ilikecake/ESP32-Wall-Display/assets/placement_back.JPG

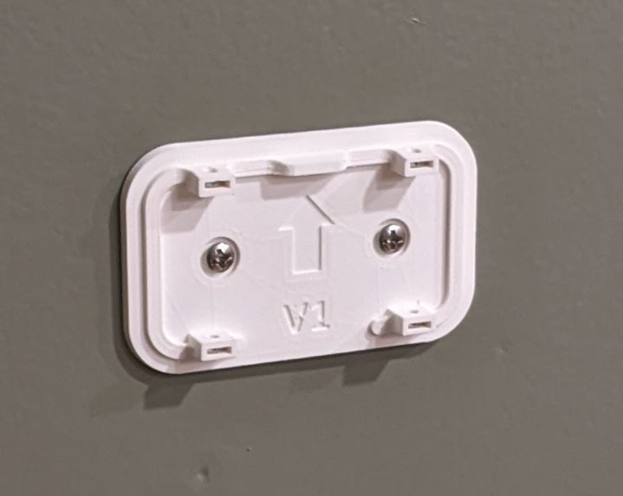
assets/placement_back.JPG
