ilikecake/ESP32-Wall-Display/assets/placement_front.JPG

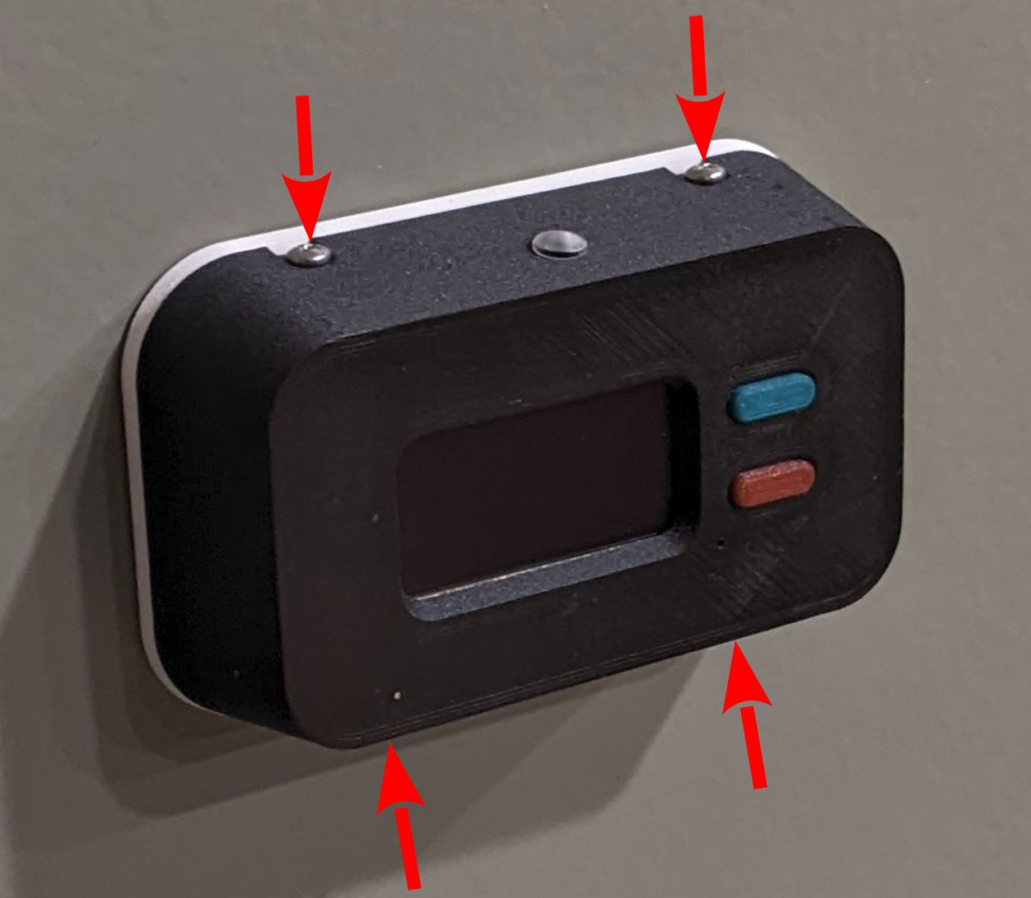
assets/placement_front.JPG
