ilikecake/ESP32-Wall-Display/assets/BOM_5.1K_Resistor.jpg

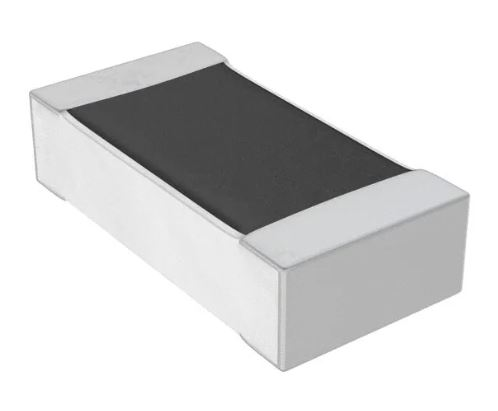
assets/BOM_5.1K_Resistor.jpg
