ilikecake/ESP32-Wall-Display/assets/BOM_Feather_ESP32-S3.jpg

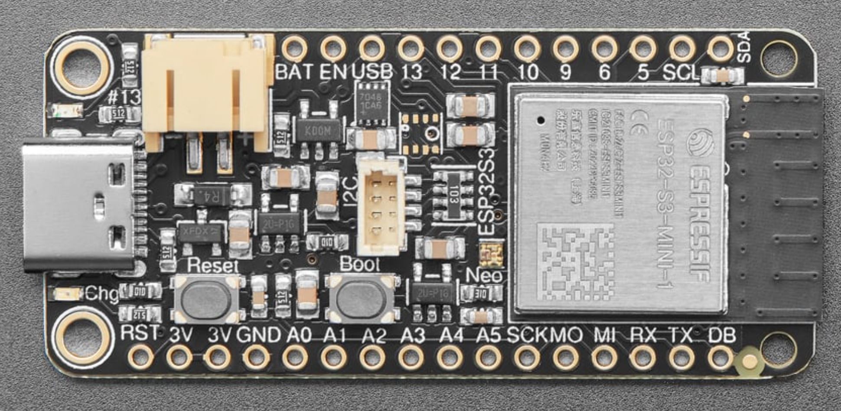
assets/BOM_Feather_ESP32-S3.jpg
