ilikecake/ESP32-Wall-Display/assets/BOM_Feather_Female_Headers.jpg

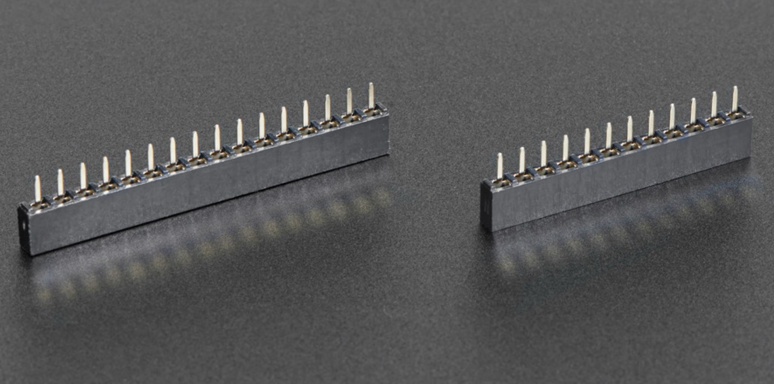
assets/BOM_Feather_Female_Headers.jpg
