ilikecake/ESP32-Wall-Display/assets/BOM_Feather_OLED_128x64.JPG

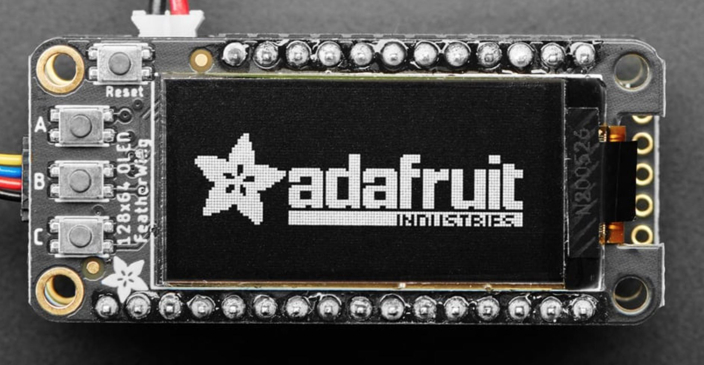
assets/BOM_Feather_OLED_128x64.JPG
