ilikecake/ESP32-Wall-Display/assets/BOM_Lightpipe.jpg

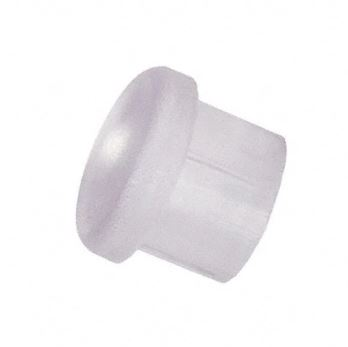
assets/BOM_Lightpipe.jpg
