ilikecake/ESP32-Wall-Display/assets/BOM_Neopixel.jpg

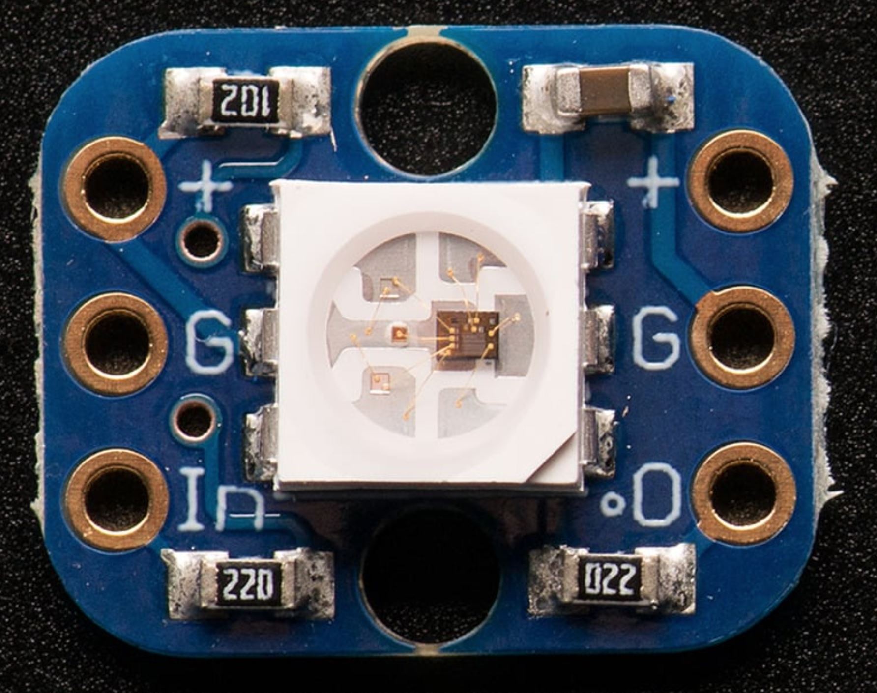
assets/BOM_Neopixel.jpg
