ilikecake/ESP32-Wall-Display/assets/BOM_Stemma_QT_Cable.jpg

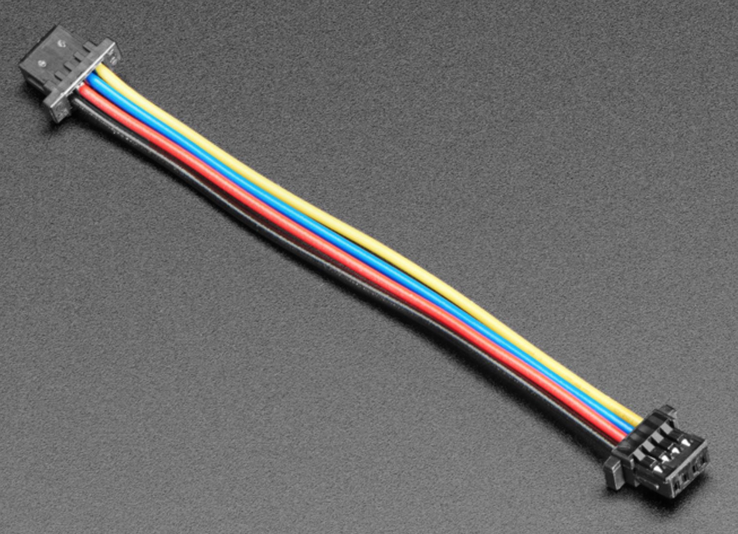
assets/BOM_Stemma_QT_Cable.jpg
