ilikecake/ESP32-Wall-Display/assets/BOM_USB_PCB.jpg

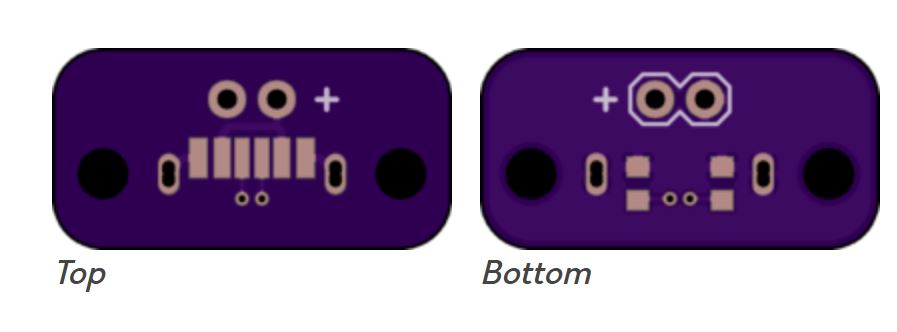
assets/BOM_USB_PCB.jpg
