ilikecake/ESP32-Wall-Display/assets/BOM_Wire.jpg

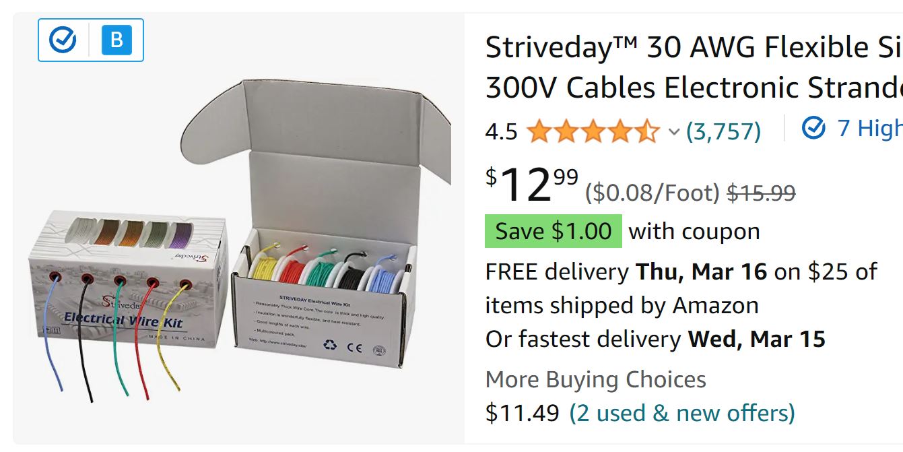
assets/BOM_Wire.jpg
