ilikecake/ESP32-Wall-Display/assets/assembly_step1_back.JPG

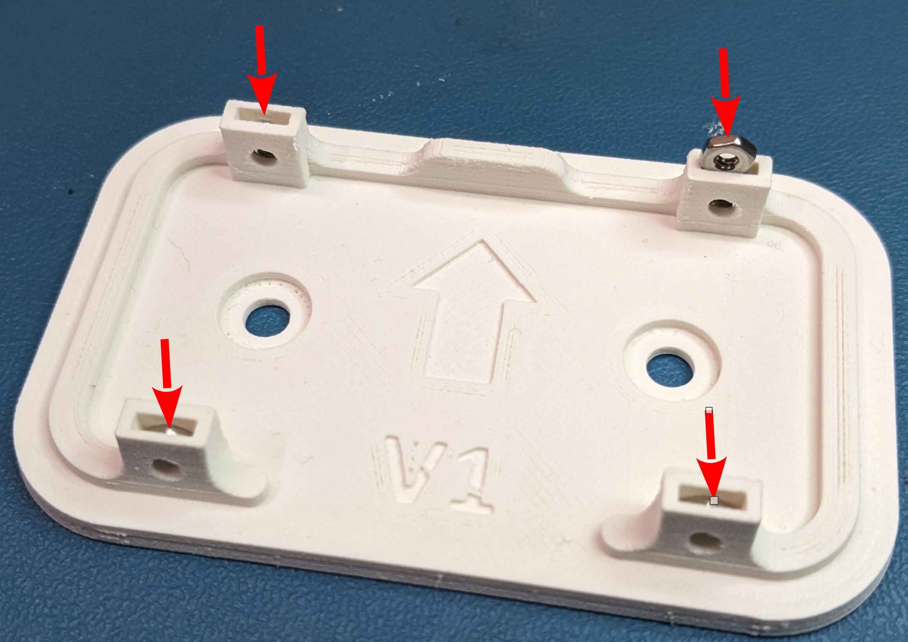
assets/assembly_step1_back.JPG
