ilikecake/ESP32-Wall-Display/assets/assembly_step1_front.JPG

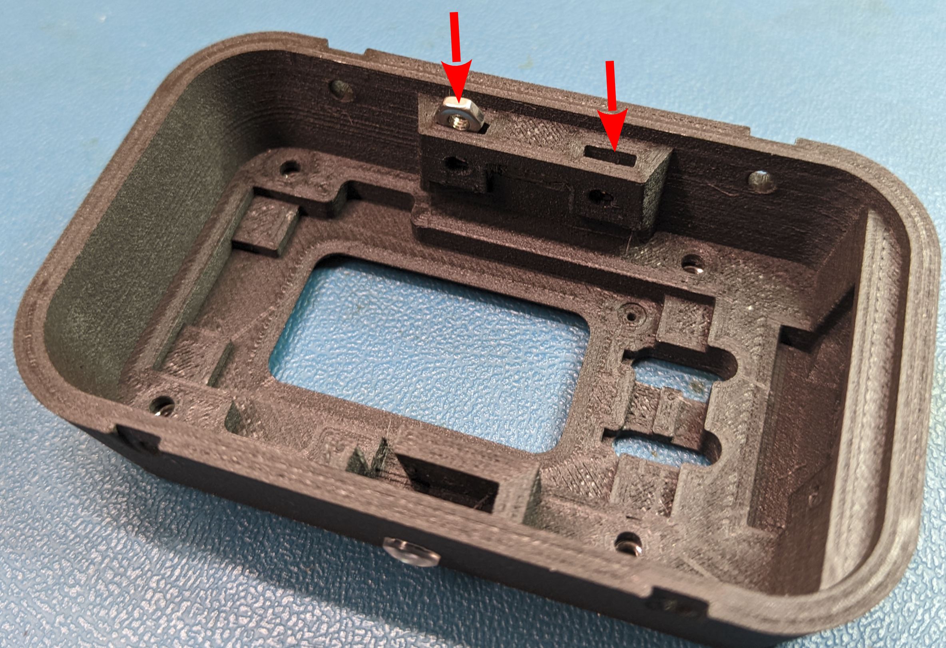
assets/assembly_step1_front.JPG
