ilikecake/ESP32-Wall-Display/assets/assembly_step2_lightpipe.JPG

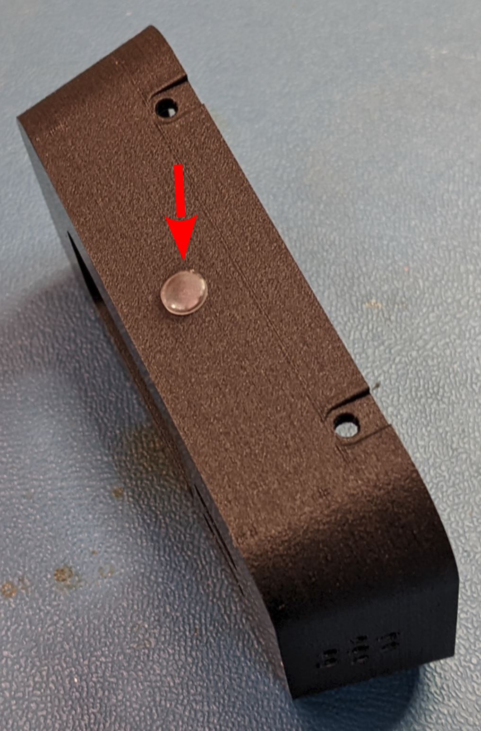
assets/assembly_step2_lightpipe.JPG
