ilikecake/ESP32-Wall-Display/assets/assembly_step3_buttons.JPG

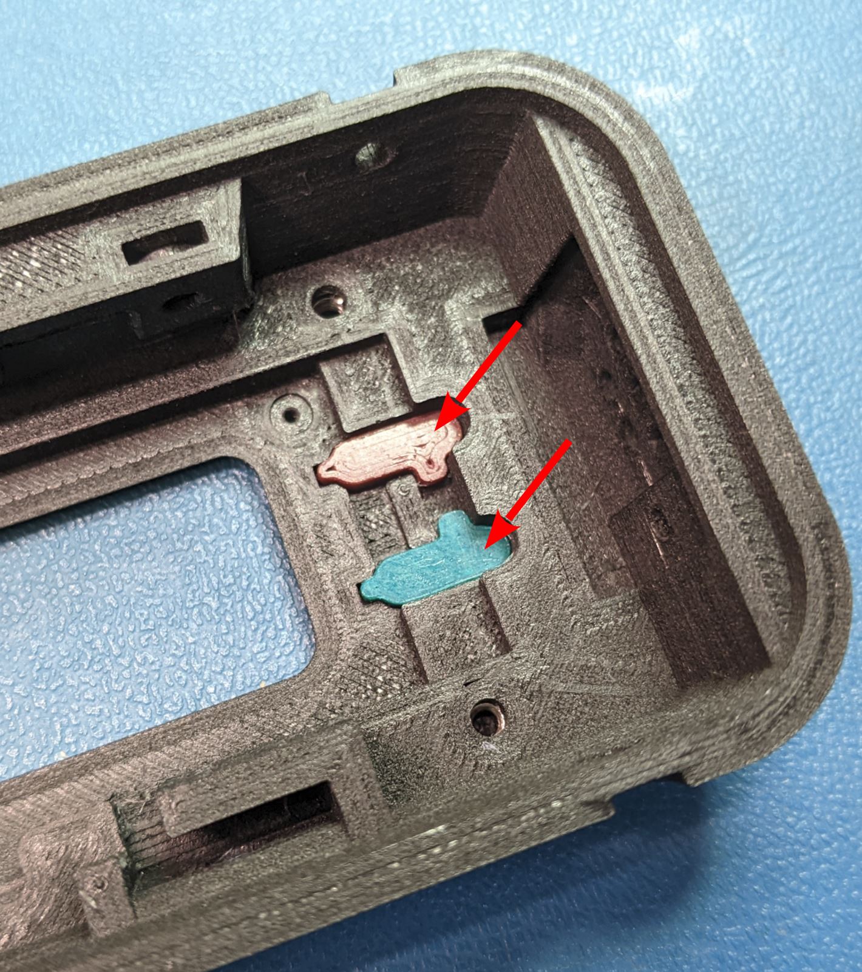
assets/assembly_step3_buttons.JPG
