ilikecake/ESP32-Wall-Display/assets/assembly_step4_power_wires.JPG

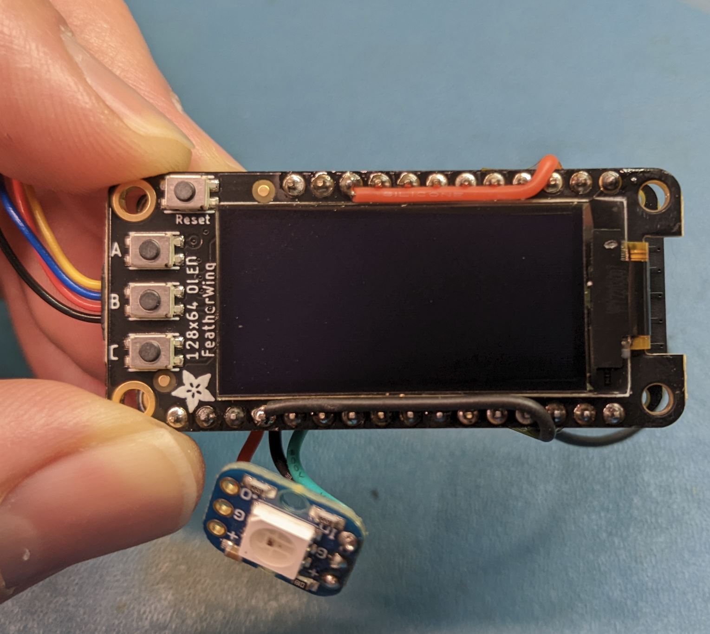
assets/assembly_step4_power_wires.JPG
