ilikecake/ESP32-Wall-Display/assets/assembly_step5_USB_port.JPG

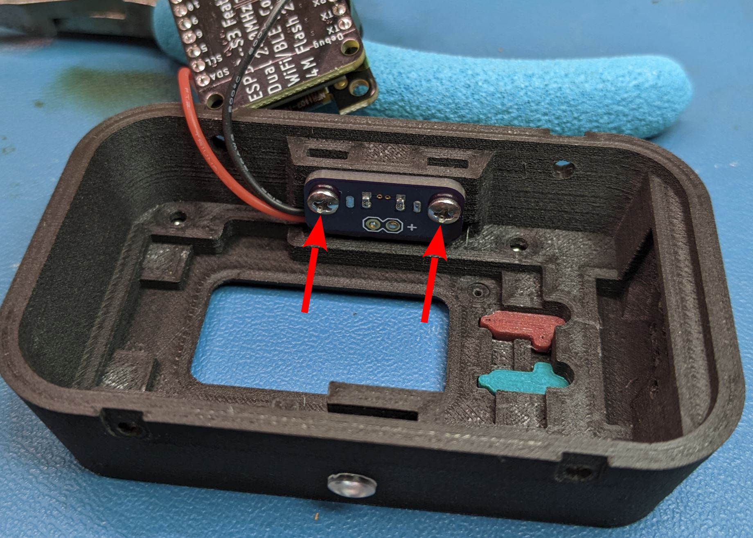
assets/assembly_step5_USB_port.JPG
