ilikecake/ESP32-Wall-Display/assets/assembly_step6_BME280.JPG

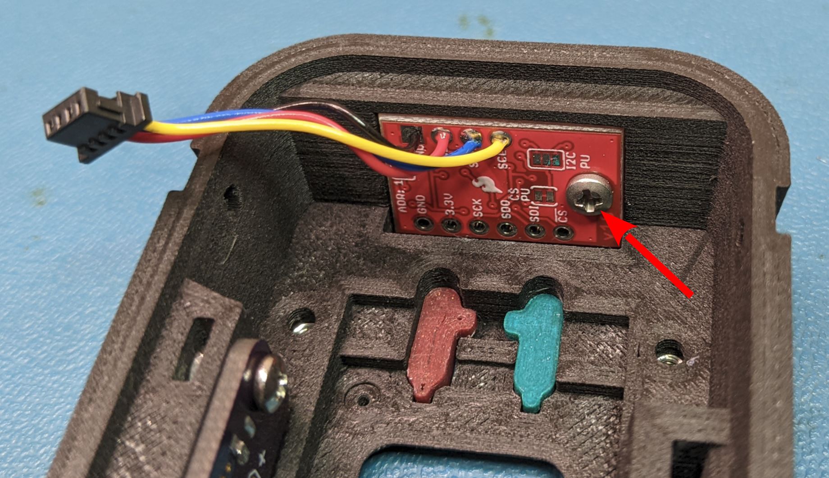
assets/assembly_step6_BME280.JPG
