ilikecake/ESP32-Wall-Display/assets/assembly_step7_display.JPG

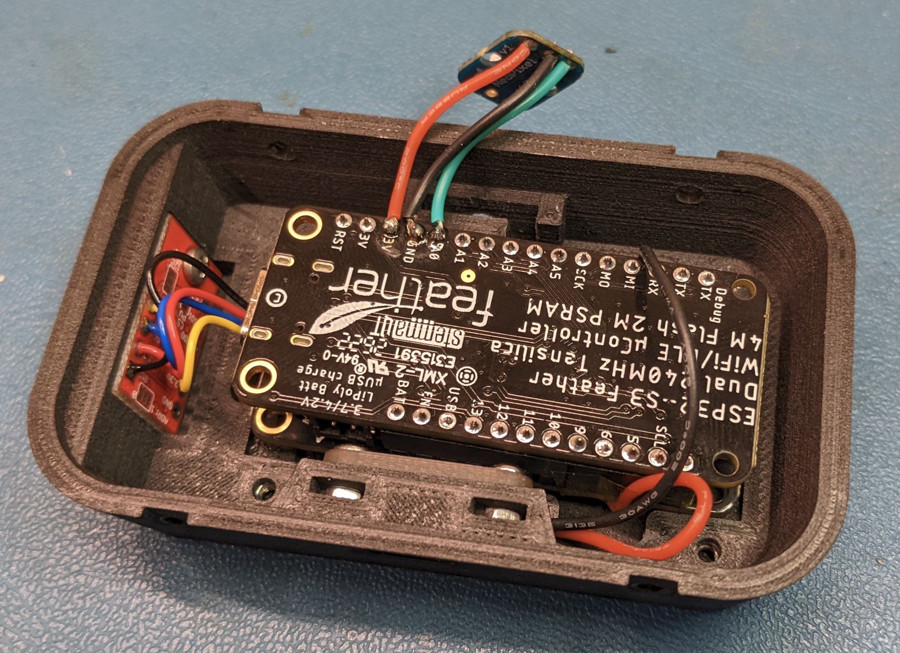
assets/assembly_step7_display.JPG
