ilikecake/ESP32-Wall-Display/assets/assembly_step7_long_support.JPG

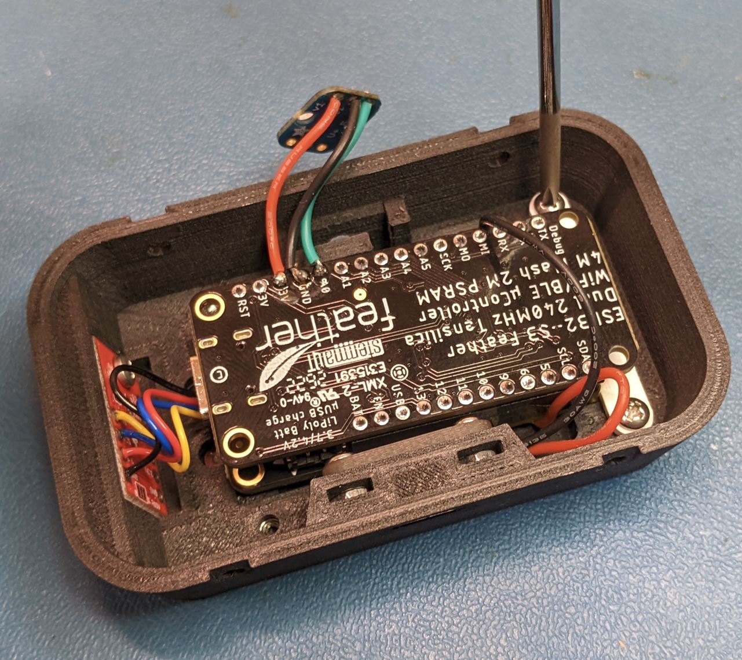
assets/assembly_step7_long_support.JPG
