ilikecake/ESP32-Wall-Display/assets/assembly_step7_short_support.JPG

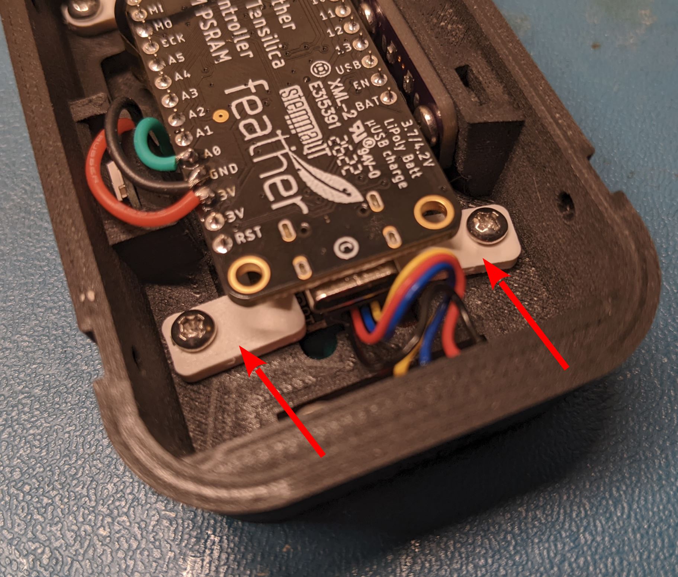
assets/assembly_step7_short_support.JPG
