ilikecake/ESP32-Wall-Display/assets/assembly_step8_LED1.JPG

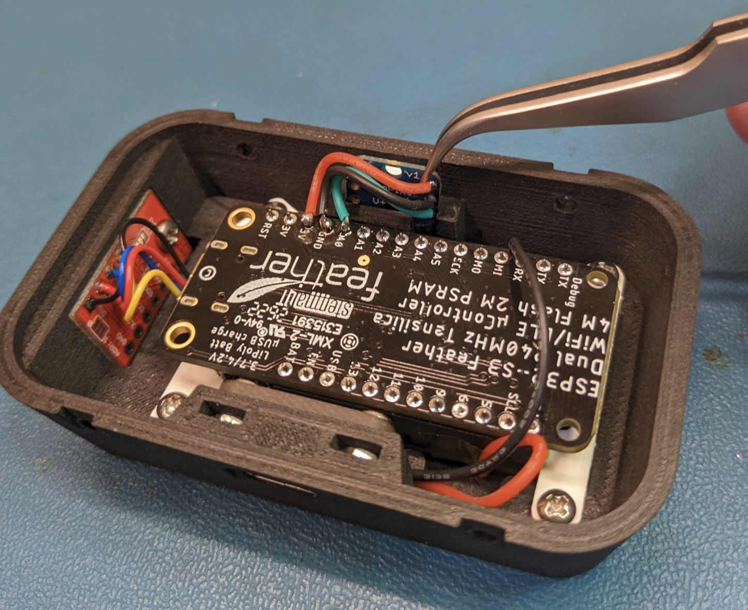
assets/assembly_step8_LED1.JPG
