ilikecake/ESP32-Wall-Display/assets/assembly_step8_LED2.JPG

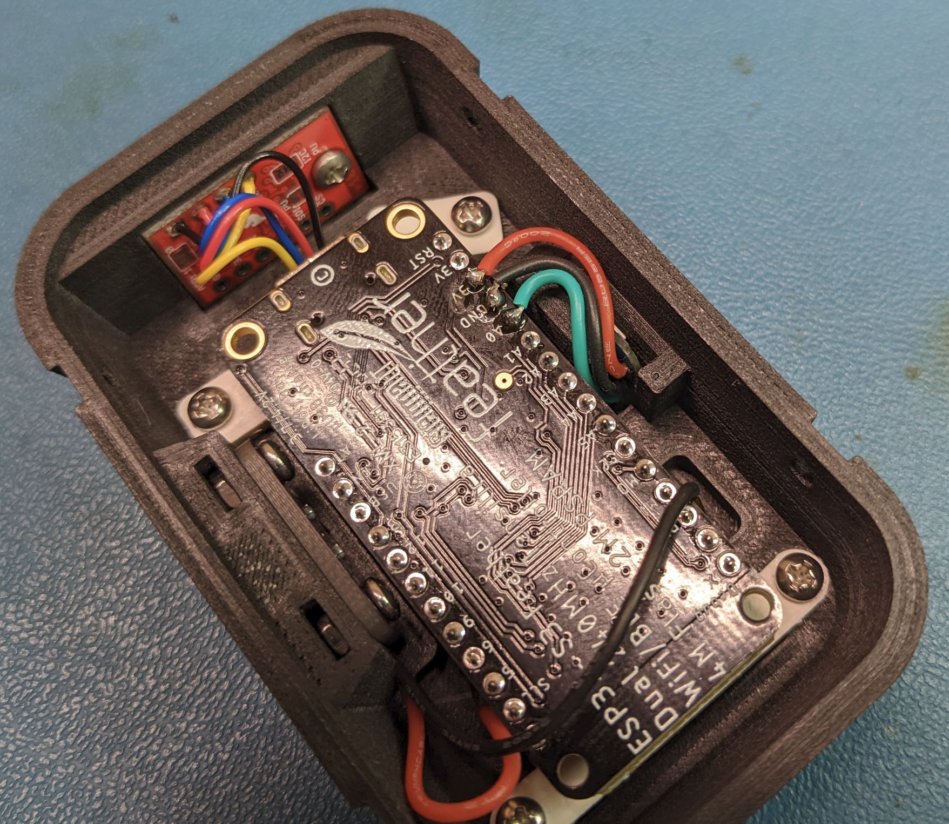
assets/assembly_step8_LED2.JPG
