ilikecake/ESP32-Wall-Display/assets/Printing_Button1.JPG

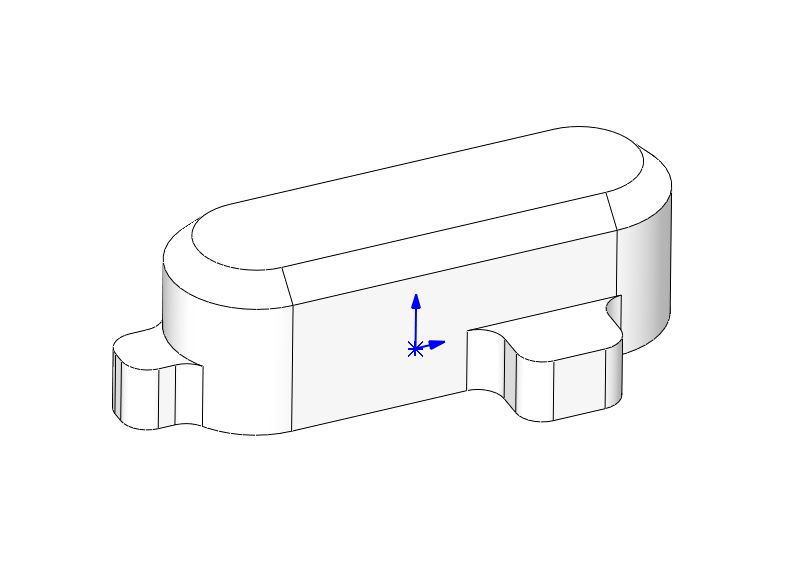
assets/Printing_Button1.JPG
