ilikecake/ESP32-Wall-Display/assets/Printing_Button2.JPG

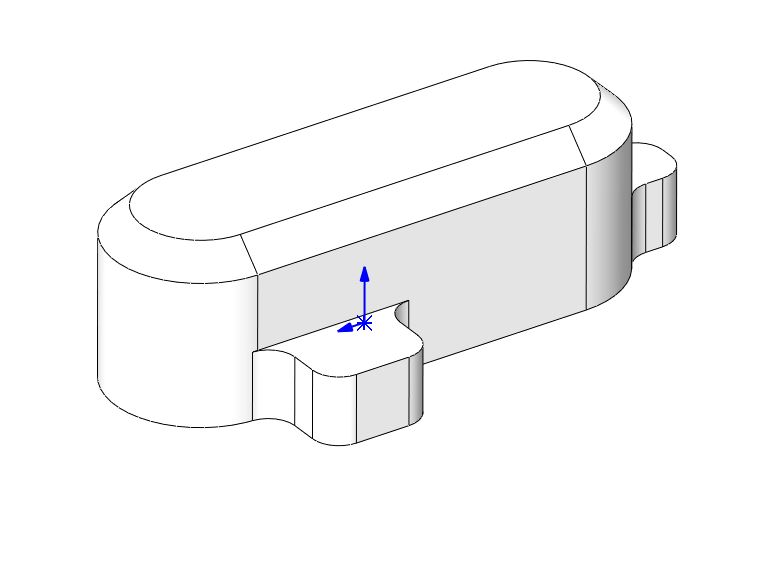
assets/Printing_Button2.JPG
