ilikecake/ESP32-Wall-Display/assets/Printing_case_front.JPG

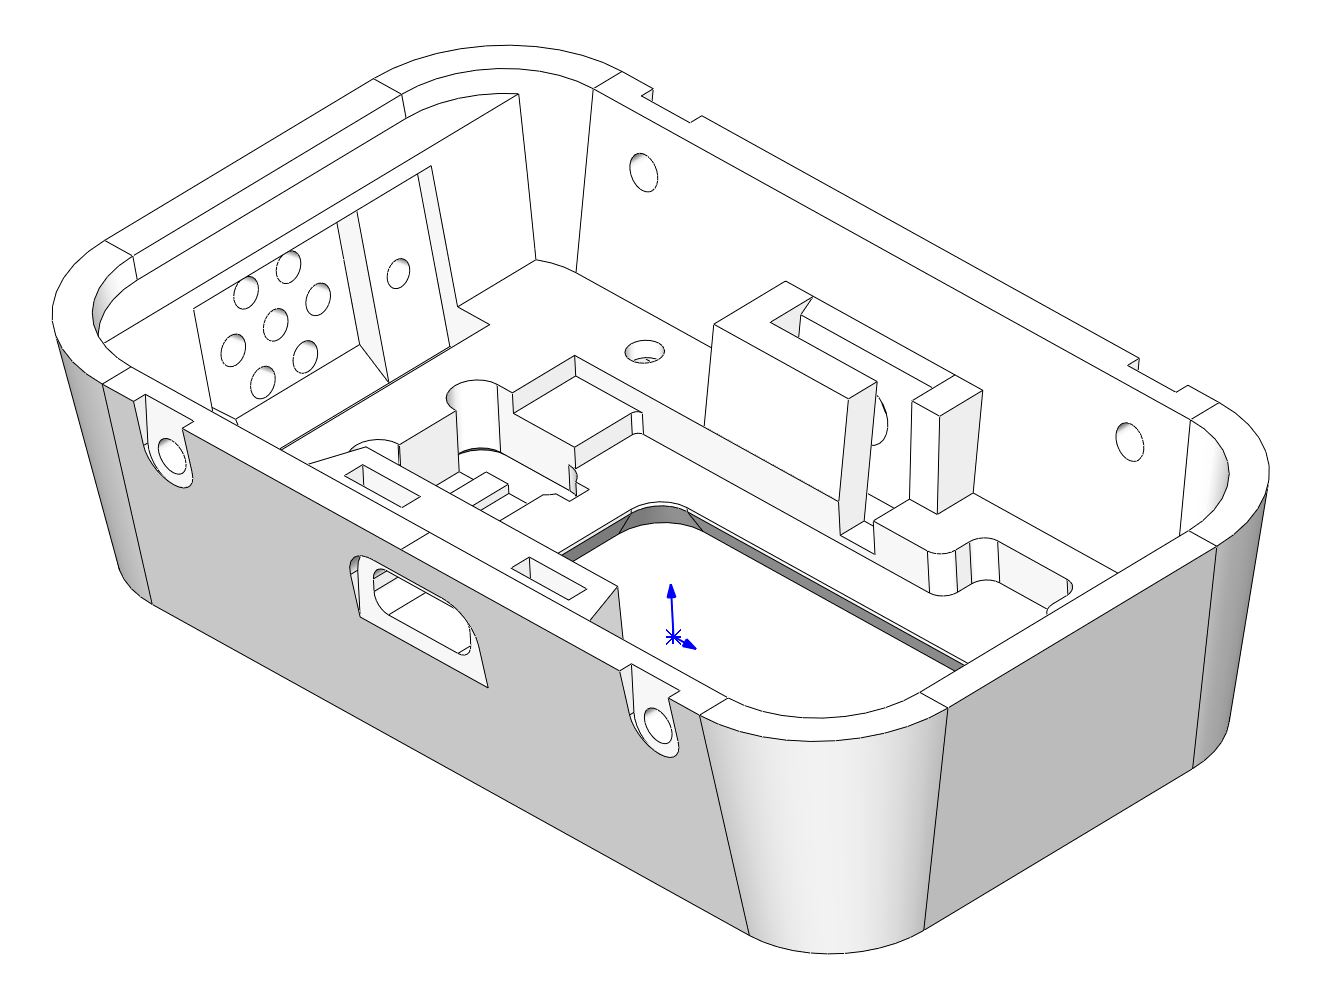
assets/Printing_case_front.JPG
