ilikecake/ESP32-Wall-Display/assets/printing_display_holder1.JPG

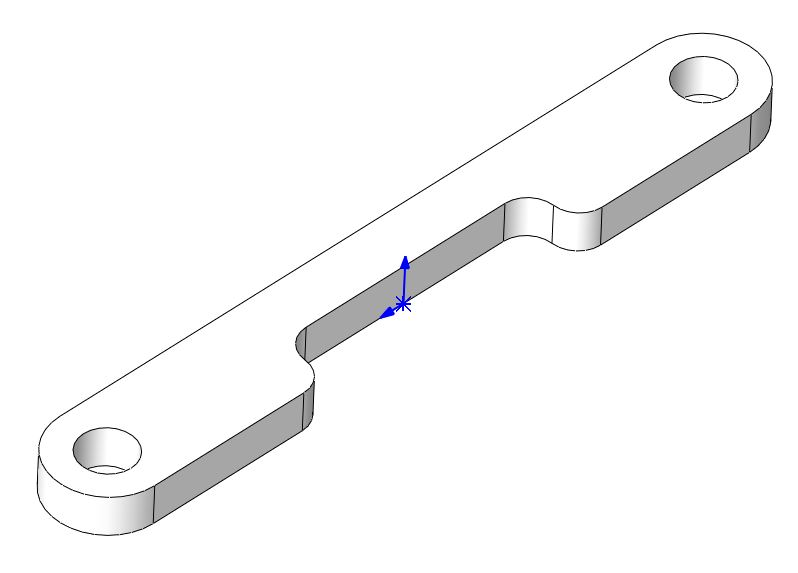
assets/printing_display_holder1.JPG
