ilikecake/ESP32-Wall-Display/assets/printing_display_holder2.JPG

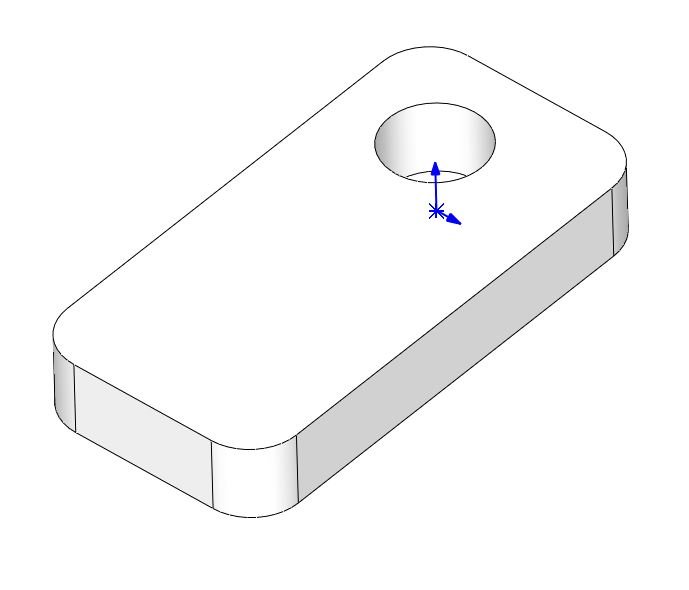
assets/printing_display_holder2.JPG
