ilikecake/ESP32-Wall-Display/assets/usage_HASS_entities.JPG

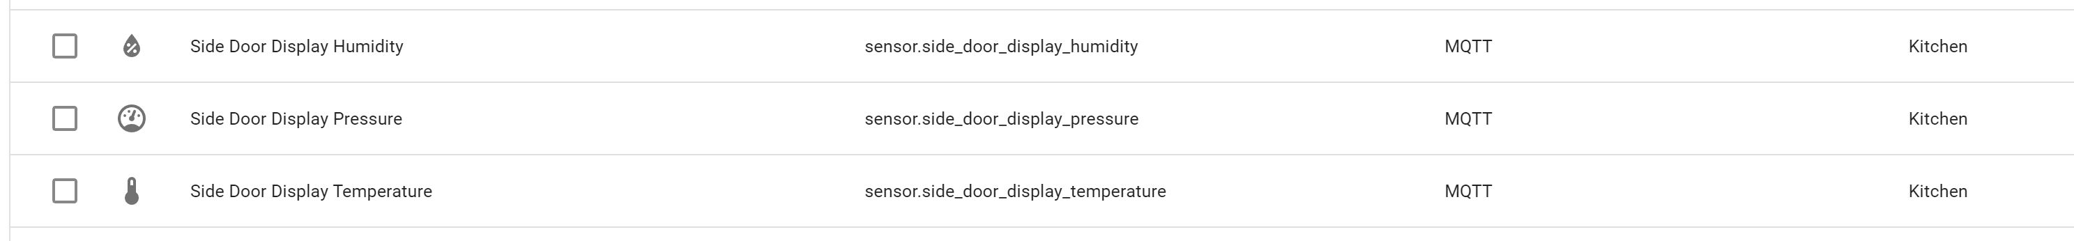
assets/usage_HASS_entities.JPG
