ilikecake/ESP32-Wall-Display/assets/usage_HASS_interface.JPG

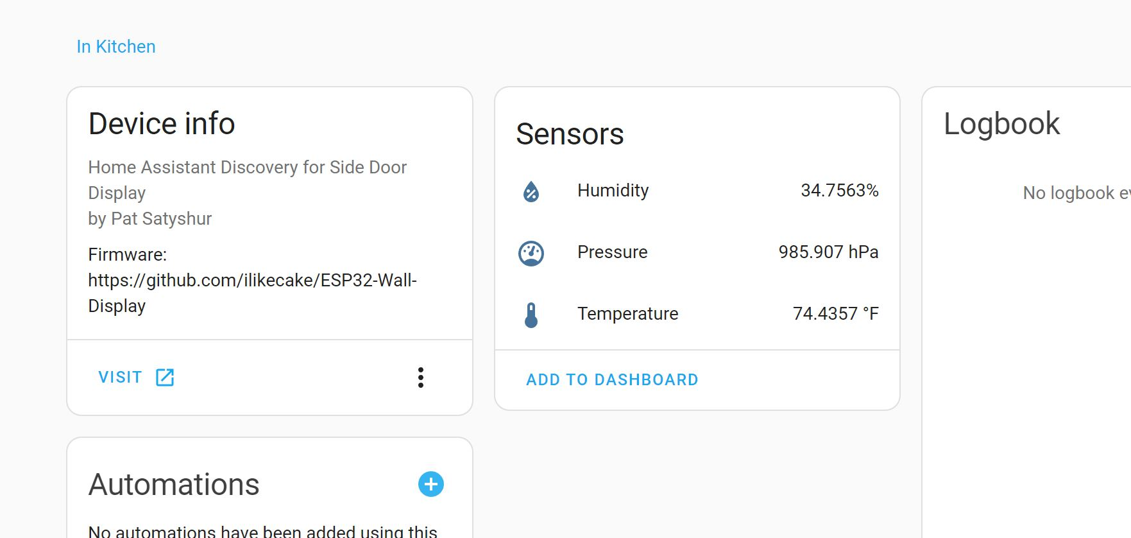
assets/usage_HASS_interface.JPG
