ilikecake/ESP32-Wall-Display/assets/usage_reset_button.JPG

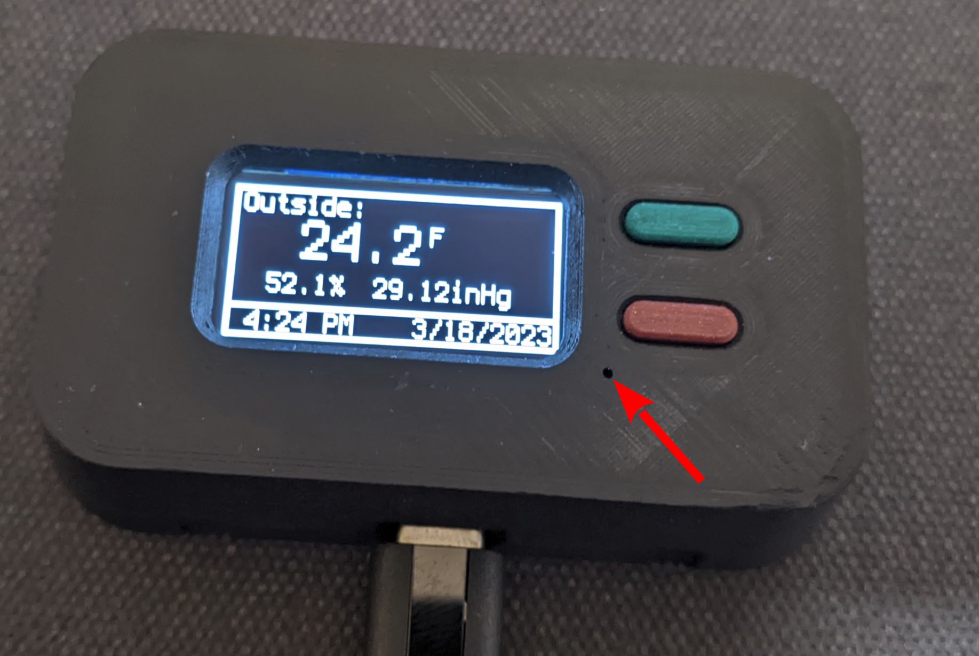
assets/usage_reset_button.JPG
