ilikecake/ESP32-Wall-Display/assets/wiring_bottom.JPG

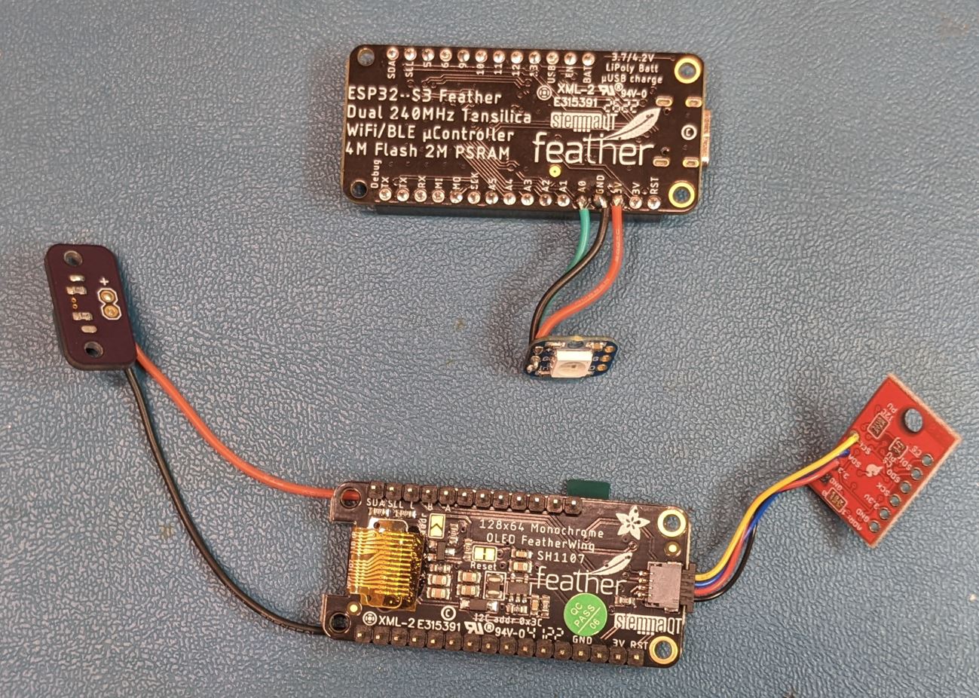
assets/wiring_bottom.JPG
