ilikecake/ESP32-Wall-Display/assets/wiring_top.JPG

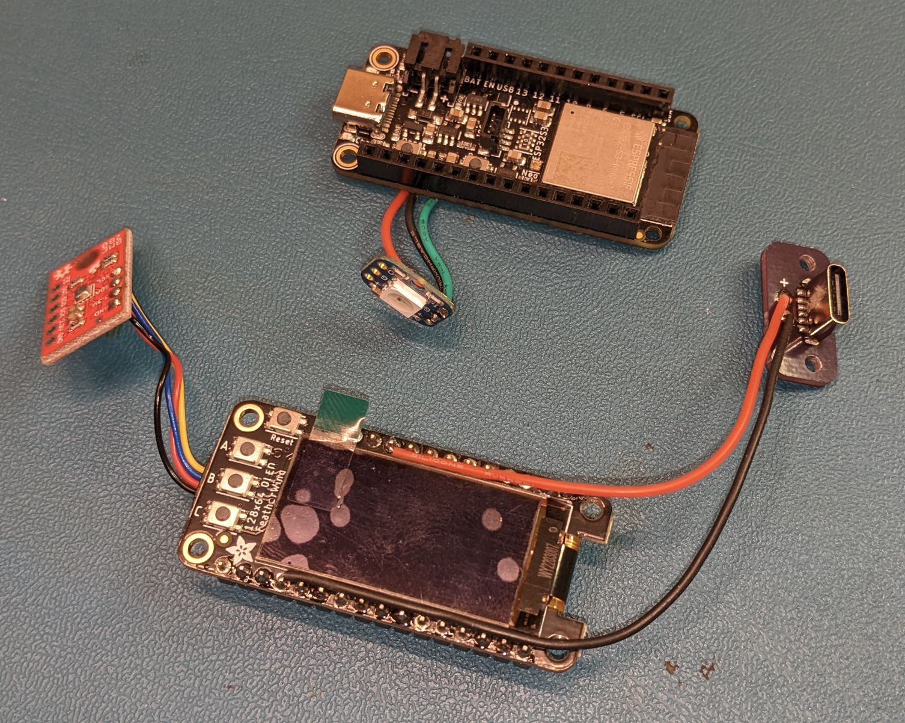
assets/wiring_top.JPG
